ITLab-CC/Sorter/3d-files/3mf/Tippything/Kurbelschleife.3mf

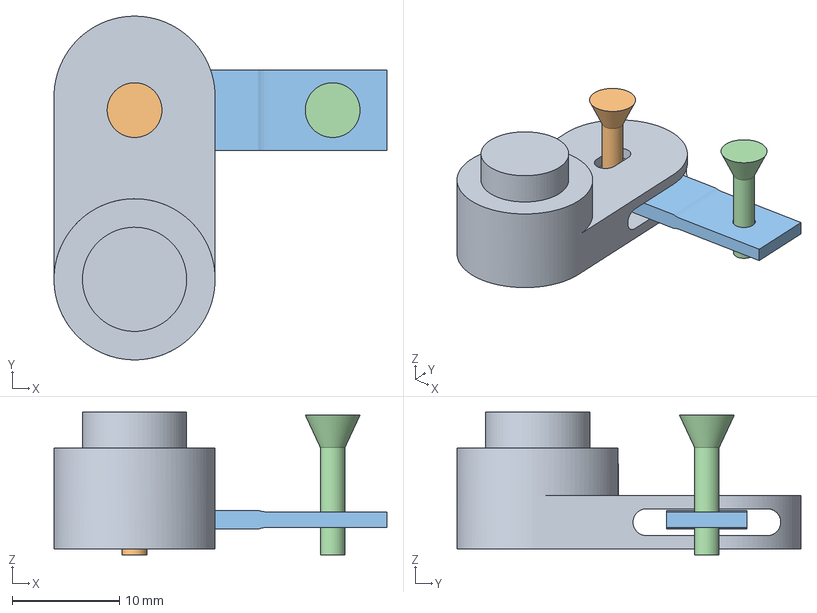
[picture p28: CAD file, 2026-06-09]
3d-files/3mf/Tippything/Kurbelschleife.3mf
31.0 x 32.0 x 13.3 mm
Körper1
Körper2
Körper5
Körper6
