ITLab-CC/Sorter/3d-files/3mf/Transporter/Tube_Curved_67.5°.3mf

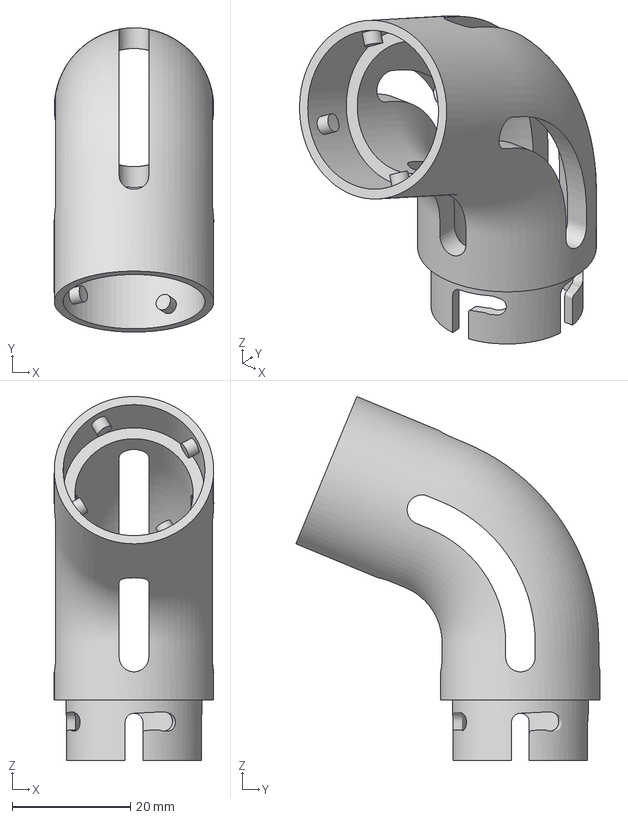
[picture p29: CAD file, 2026-06-09]
3d-files/3mf/Transporter/Tube_Curved_67.5°.3mf
27.0 x 51.5 x 61.6 mm
