ITLab-CC/Sorter/3d-files/3mf/Kamera/Kameraholder.3mf

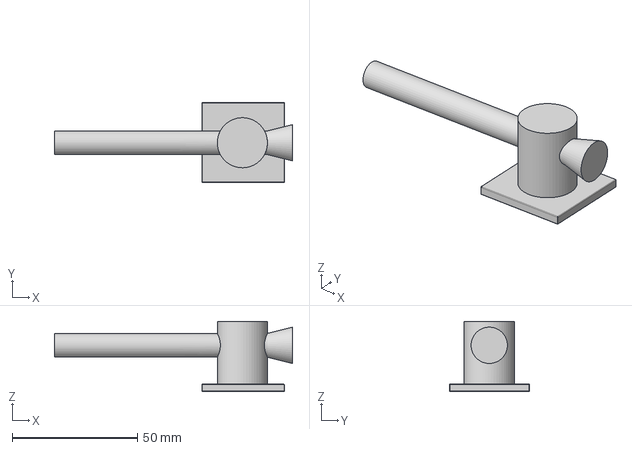
[picture p30: CAD file, 2026-06-09]
3d-files/3mf/Kamera/Kameraholder.3mf
95.0 x 32.0 x 28.0 mm
