ITLab-CC/Sorter/3d-files/3mf/Tippything/Tippything_Case.3mf

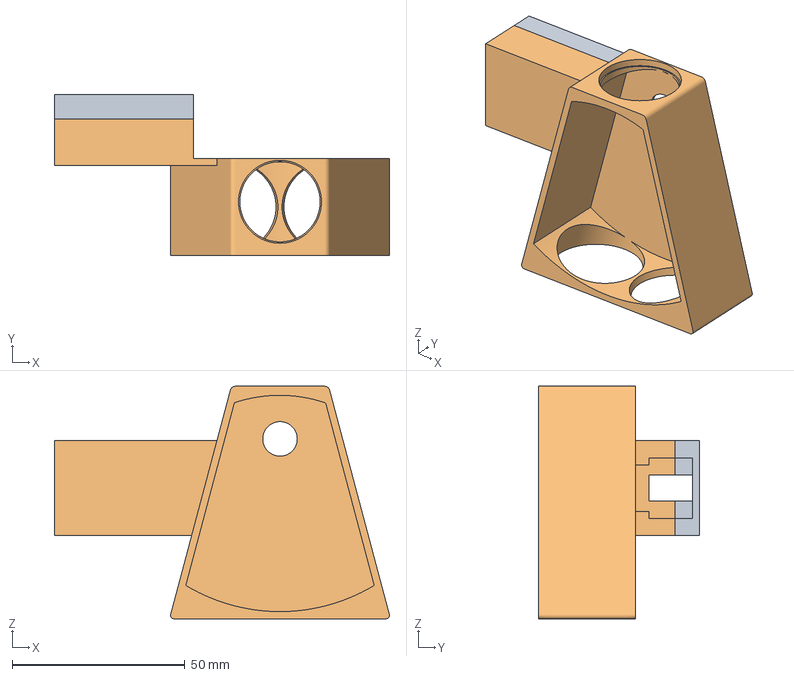
[picture p31: CAD file, 2026-06-09]
3d-files/3mf/Tippything/Tippything_Case.3mf
96.9 x 46.5 x 67.3 mm
Solenoid_Case
Tippything
