ITLab-CC/Sorter/3d-files/3mf/Transporter/Tube_Curved_90°.3mf

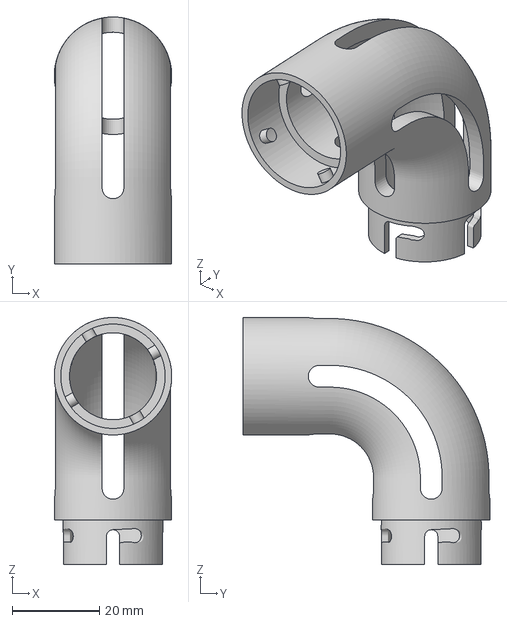
[picture p32: CAD file, 2026-06-09]
3d-files/3mf/Transporter/Tube_Curved_90°.3mf
27.0 x 56.8 x 56.8 mm
