ITLab-CC/Sorter/3d-files/3mf/Tippything/Plexiglashalter.3mf

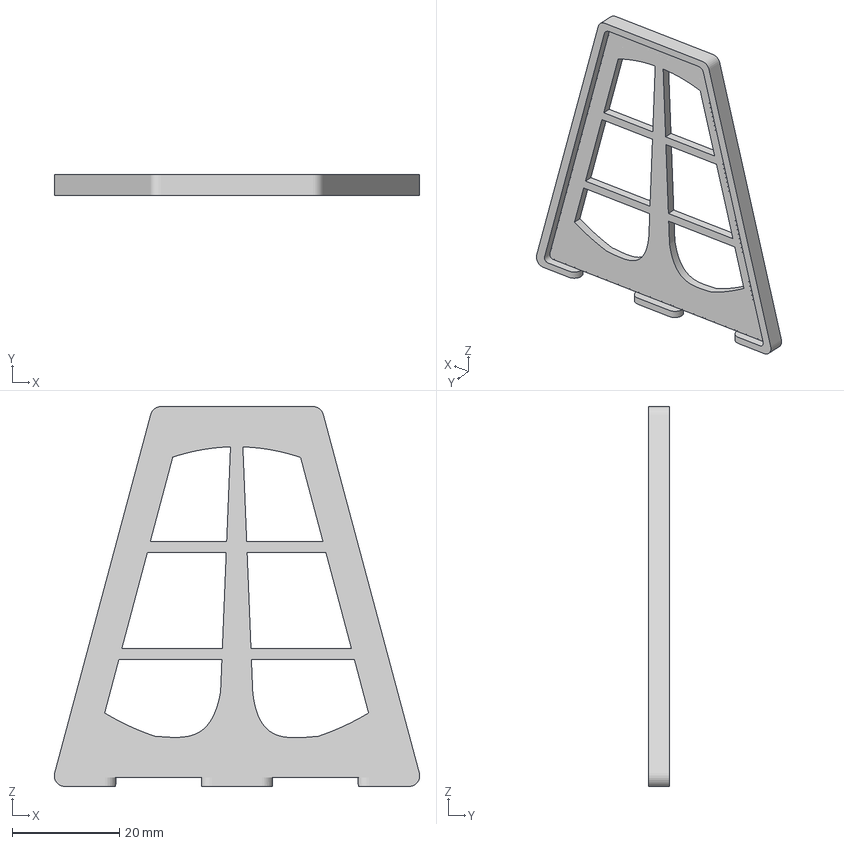
[picture p33: CAD file, 2026-06-09]
3d-files/3mf/Tippything/Plexiglashalter.3mf
68.3 x 4.00 x 71.0 mm
