ITLab-CC/Sorter/3d-files/3mf/Transporter/Transporter_Adapter.3mf

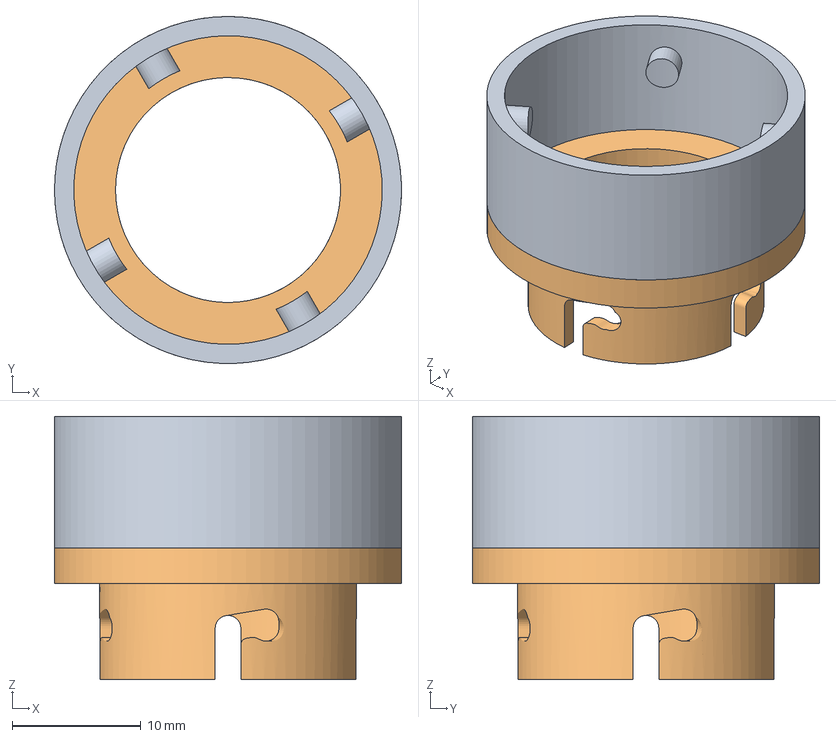
[picture p34: CAD file, 2026-06-09]
3d-files/3mf/Transporter/Transporter_Adapter.3mf
27.0 x 27.0 x 20.5 mm
Tube (1)
Tube
