ITLab-CC/Sorter/3d-files/3mf/Tippything/Box.3mf

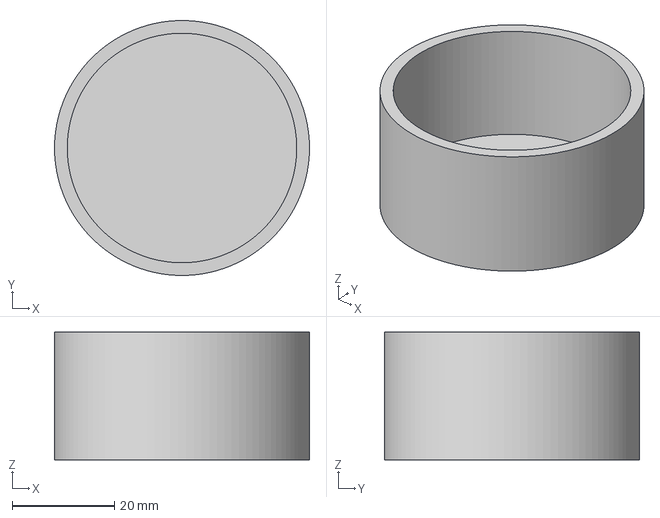
[picture p35: CAD file, 2026-06-09]
3d-files/3mf/Tippything/Box.3mf
50.0 x 50.0 x 25.0 mm
