ITLab-CC/Sorter/3d-files/3mf/Transporter/Tube_Straight.3mf

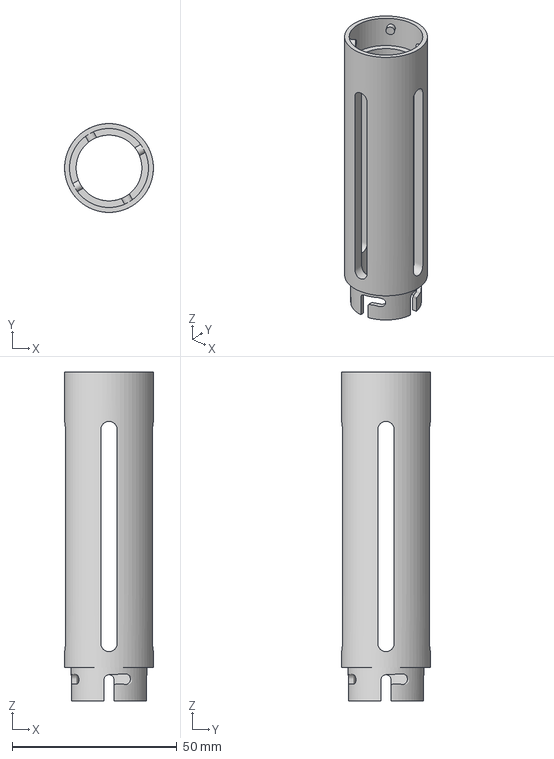
[picture p36: CAD file, 2026-06-09]
3d-files/3mf/Transporter/Tube_Straight.3mf
27.0 x 27.0 x 100.0 mm
