ITLab-CC/Sorter/3d-files/3mf/Tippything/Track.3mf

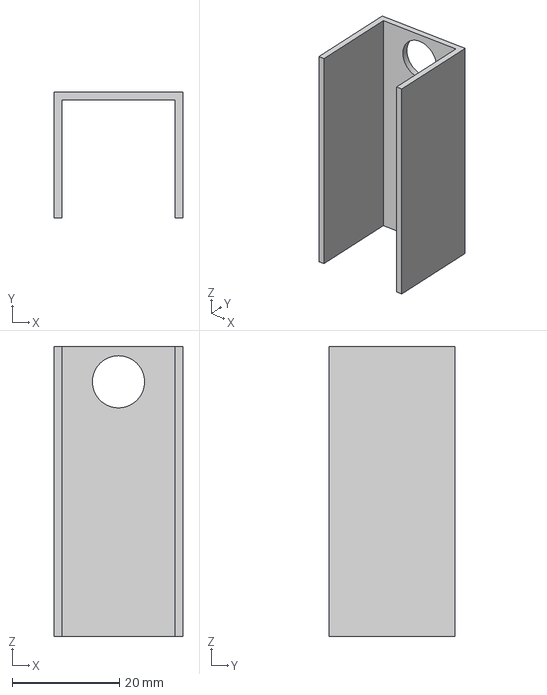
[picture p37: CAD file, 2026-06-09]
3d-files/3mf/Tippything/Track.3mf
24.0 x 23.5 x 54.0 mm
