ITLab-CC/Sorter/3d-files/3mf/Transporter/Motor_Holder.3mf

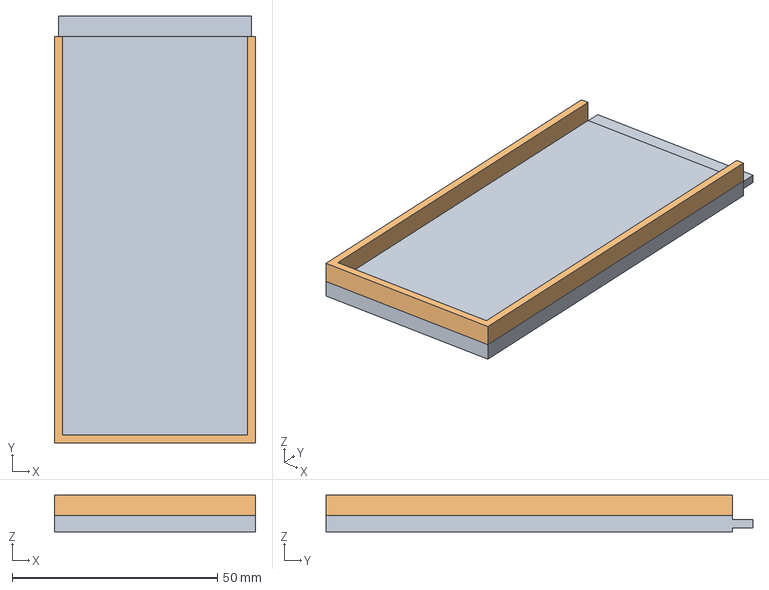
[picture p38: CAD file, 2026-06-09]
3d-files/3mf/Transporter/Motor_Holder.3mf
49.0 x 104.0 x 9.00 mm
Boden
Wand
